rayvburn/diff_drive_mapping_robot/diff_drive_mapping_robot_controller/config/controller_params.yaml

# PID Controller parameters

Kp: 1.0
Ki: 6.0
Kd: 0.0

upper_limit:  60   # should be a little bigger than max ang vel from base controller
lower_limit: -60
windup_limit: 15

min_loop_frequency: 50.0
max_loop_frequency: 125.0

# topic_from_controller: "/robot/wheel_left/cmd_vel/closed_loop"   # needs to be remapped for each wheel
# topic_from_plant:      "/robot/wheel_left/velocity/angular"      # needs to be remapped for each wheel
# setpoint_topic:        "/robot/wheel_left/cmd_vel/open_loop"     # needs to be remapped for each wheel
